kingsmanayan/LoRa-Based-Pet-Tracking-Collar/part1-hardware/bridge/LoRa_Reciver_End_Bridge_part/LORA_Bridge_part.kicad_sch

## KiCad design part1-hardware/bridge/LoRa_Reciver_End_Bridge_part/LORA_Bridge_part.kicad_sch (2026-09-05)

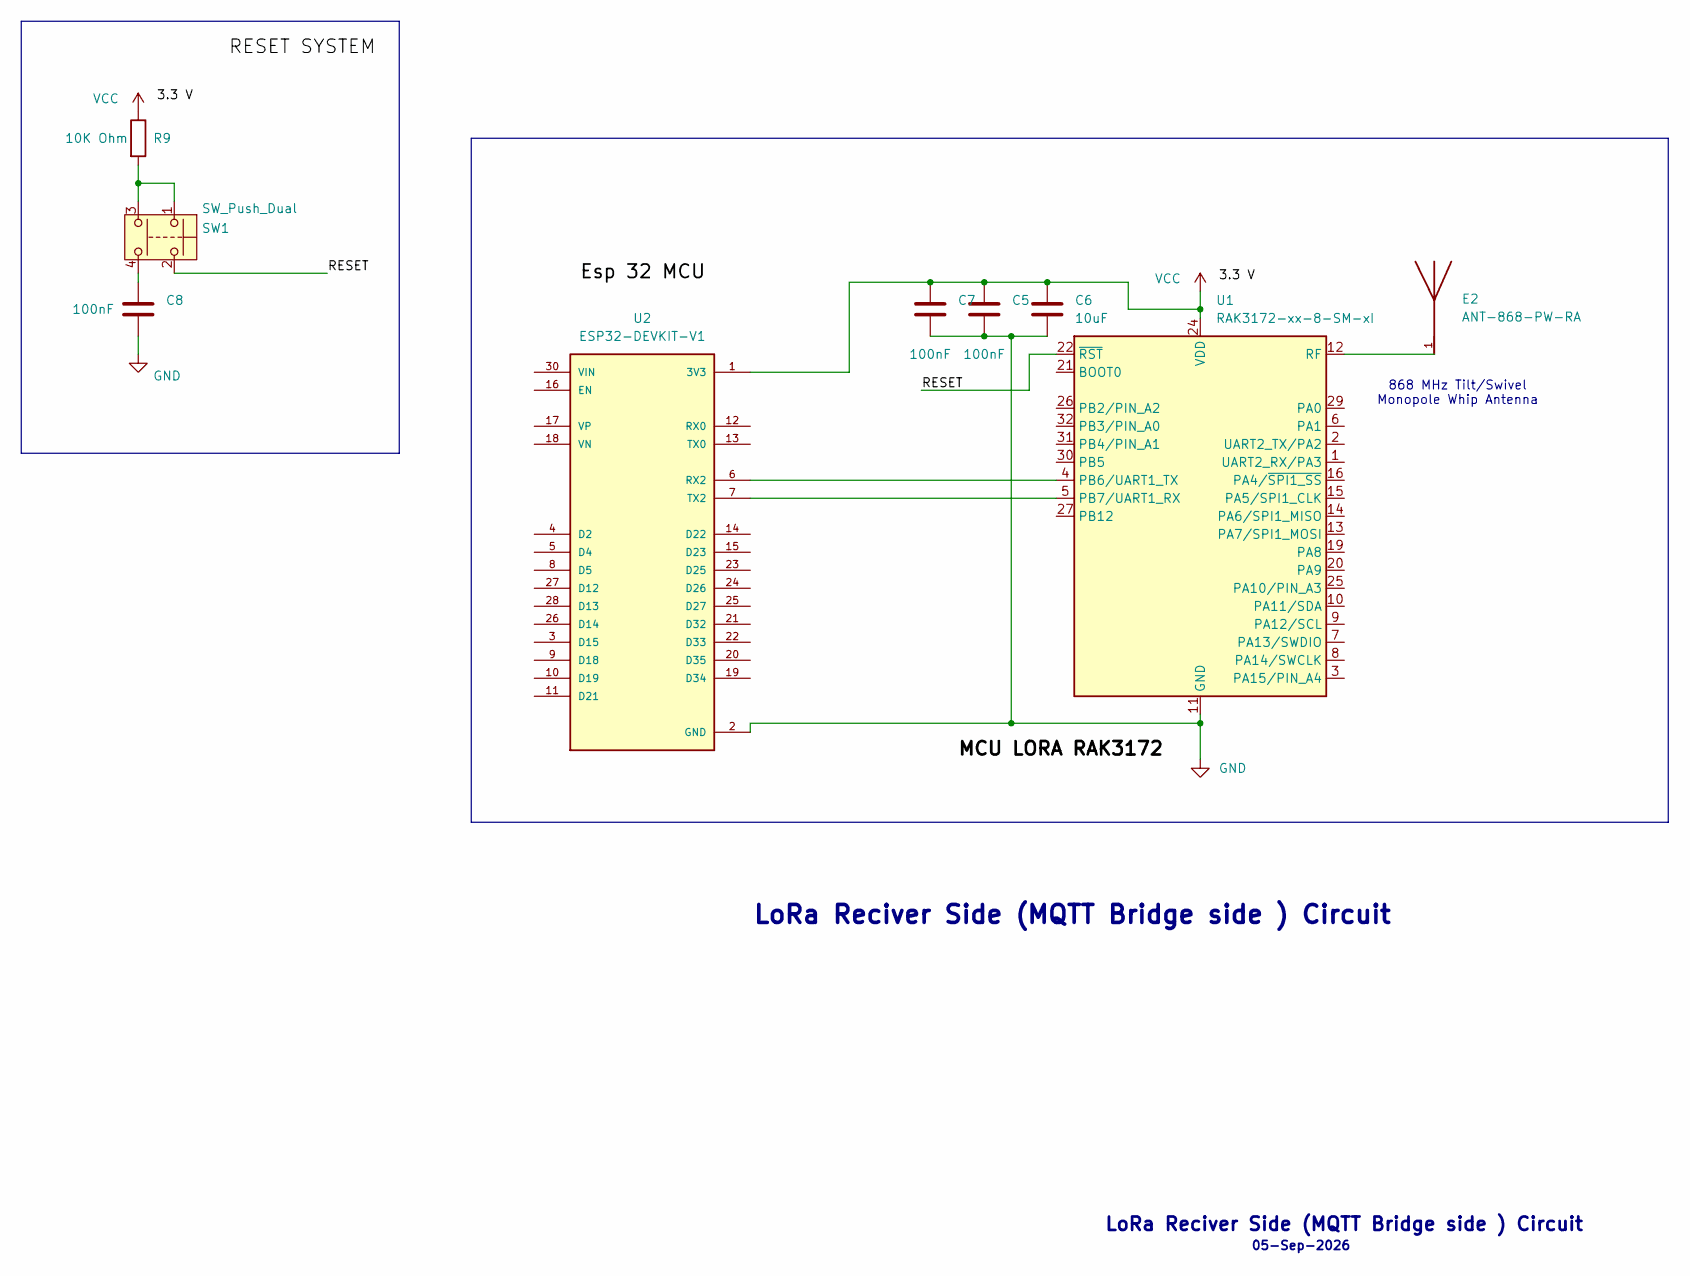
[picture p9: schematic LORA_Bridge_part.kicad_sch]

Parts:
C5, C7, C8: 100nF
C6: 10uF
E2: ANT-868-PW-RA; XDCR_ANT-868-PW-RA; PARTREV 12/9/13
R9: 10K Ohm
SW1: SW_Push_Dual; Nidec_Copal_CAS-120A
U1: RAK3172-xx-8-SM-xI; RAK3172
U2: ESP32-DEVKIT-V1; MODULE_ESP32_DEVKIT_V1; PARTREV N/A

Connections:
GND: C5.2, C6.2, C7.2, C8.2, U1.11 (GND), U1.17 (GND), U1.18 (GND), U1.23 (GND), U1.28 (GND), U2.2 (GND), U2.29 (GND)
unnamed: C8.1, SW1.4
unnamed: E2.1, E2.2, U1.12 (RF)
unnamed: R9.2, SW1.1, SW1.3
unnamed: U1.4 (PB6/UART1_TX), U2.6 (RX2)
unnamed: U1.5 (PB7/UART1_RX), U2.7 (TX2)
RESET: SW1.2, U1.22 (~RST)
VCC: C5.1, C6.1, C7.1, R9.1, U1.24 (VDD), U2.1 (3V3)

Notes on the sheet:
868 MHz Tilt/Swivel Monopole Whip Antenna
LoRa Reciver Side (MQTT Bridge side ) Circuit
05-Sep-2026
