kingsmanayan/LoRa-Based-Pet-Tracking-Collar/part1-hardware/collar/LoRa_Based_Pet_Collar/LoRa_Based_Pet_Collar.kicad_sch

## KiCad design part1-hardware/collar/LoRa_Based_Pet_Collar/LoRa_Based_Pet_Collar.kicad_sch (2026-09-05)

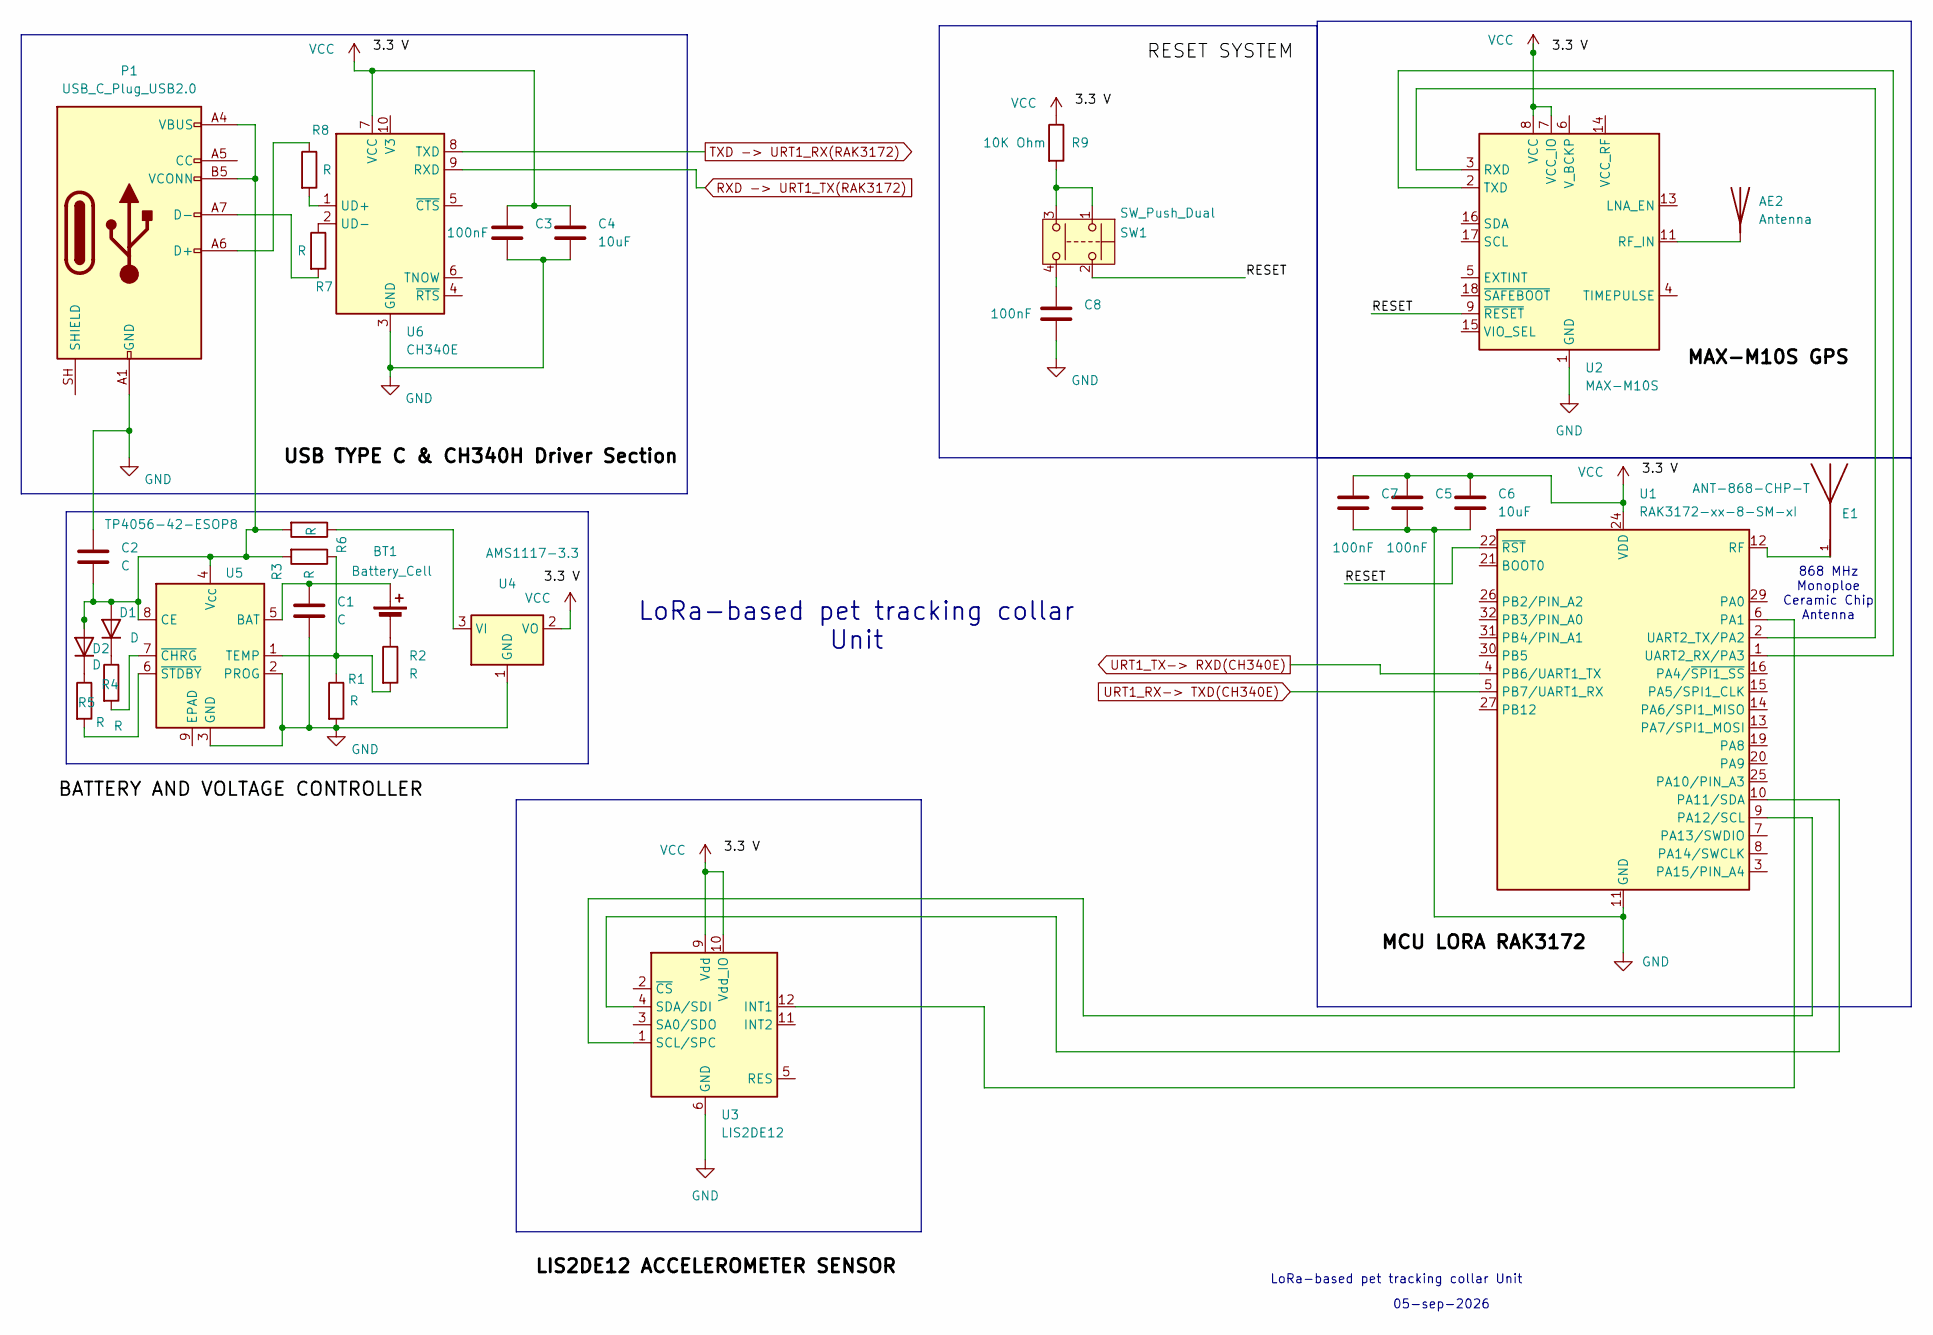
[picture p10: schematic LoRa_Based_Pet_Collar.kicad_sch]

Parts:
AE2: Antenna; DFN-8-1EP_2x3mm_P0.5mm_EP0.61x2.2mm
BT1: Battery_Cell; QFN-40-1EP_6x6mm_P0.5mm_EP4.6x4.6mm
C1, C2: C
C3, C5, C7, C8: 100nF
C4, C6: 10uF
D1, D2: D
E1: ANT-868-CHP-T; XDCR_ANT-868-CHP-T; PARTREV C
P1: USB_C_Plug_USB2.0; WDFN-10-1EP_3x3mm_P0.5mm_EP1.8x2.5mm
R1, R2, R3, R4, R5, R6, R7, R8: R
R9: 10K Ohm
SW1: SW_Push_Dual; Nidec_Copal_CAS-120A
U1: RAK3172-xx-8-SM-xI; RAK3172
U2: MAX-M10S; ublox_MAX
U3: LIS2DE12; LGA-12_2x2mm_P0.5mm
U4: AMS1117-3.3; SOT-223-3_TabPin2
U5: TP4056-42-ESOP8; SOIC-8-1EP_3.9x4.9mm_P1.27mm_EP2.41x3.3mm_ThermalVias
U6: CH340E; MSOP-10_3x3mm_P0.5mm

Connections:
GND: C1.2, C2.1, C3.2, C4.2, C5.2, C6.2, C7.2, C8.2, P1.A1 (GND), P1.A12 (GND), P1.B1 (GND), P1.B12 (GND), R1.2, U1.11 (GND), U1.17 (GND), U1.18 (GND), U1.23 (GND), U1.28 (GND), U2.1 (GND), U2.10 (GND), U2.12 (GND), U3.6 (GND), U3.7 (GND), U3.8 (GND), U4.1 (GND), U5.2 (PROG), U5.3 (GND), U6.3 (GND)
unnamed: AE2.1, U2.11 (RF_IN)
unnamed: BT1.1 (+), C1.1, U5.5 (BAT)
unnamed: BT1.2 (-), R2.1
unnamed: C2.2, D1.2 (A), D2.2 (A), P1.A4 (VBUS), P1.A9 (VBUS), P1.B4 (VBUS), P1.B5 (VCONN), P1.B9 (VBUS), R3.2, R6.2, U5.4 (V_{CC}), U5.8 (CE)
unnamed: C8.1, SW1.4
unnamed: D1.1 (K), R4.1
unnamed: D2.1 (K), R5.1
unnamed: E1.1, U1.12 (RF)
unnamed: P1.A6 (D+), R8.1
unnamed: P1.A7 (D-), R7.2
unnamed: R1.1, R2.2, R3.1, U5.1 (TEMP)
unnamed: R4.2, U5.7 (~CHRG)
unnamed: R5.2, U5.6 (~STDBY)
unnamed: R6.1, U4.3 (VI)
unnamed: R7.1, U6.2 (UD-)
unnamed: R8.2, U6.1 (UD+)
unnamed: R9.2, SW1.1, SW1.3
unnamed: U1.1 (UART2_RX/PA3), U2.2 (TXD)
unnamed: U1.2 (UART2_TX/PA2), U2.3 (RXD)
unnamed: U1.6 (PA1), U3.12 (INT1)
unnamed: U1.9 (PA12/SCL), U3.1 (SCL/SPC)
unnamed: U1.10 (PA11/SDA), U3.4 (SDA/SDI)
RESET: SW1.2, U1.22 (~RST), U2.9 (~RESET)
RXD -> URT1_TX(RAK3172): U6.9 (RXD)
TXD -> URT1_RX(RAK3172): U6.8 (TXD)
URT1_RX-> TXD(CH340E): U1.5 (PB7/UART1_RX)
URT1_TX-> RXD(CH340E): U1.4 (PB6/UART1_TX)
VCC: C3.1, C4.1, C5.1, C6.1, C7.1, R9.1, U1.24 (VDD), U2.7 (VCC_IO), U2.8 (VCC), U3.9 (Vdd), U3.10 (Vdd_IO), U4.2 (VO), U6.7 (VCC)

Notes on the sheet:
LoRa-based pet tracking collar Unit
868 MHz Monoploe Ceramic Chip Antenna
05-sep-2026
LoRa-based pet tracking collar Unit
